Abestanis/BalloonLaserPointing/src/SerialConnection.cpp

#include "arduinoSystem.h"
#include "SerialConnection.h"


/** The first byte of a message header, used to detect the start of the header */
constexpr uint8_t SYNC_BYTE_1 = 0xAA;
/** The second byte of a message header, used to detect the start of the header */
constexpr uint8_t SYNC_BYTE_2 = 0x55;

/**
 * The structure of a GPS message.
 */
typedef struct [[gnu::packed]] {
    /** The latitude in degrees. */
    double latitude;
    /** The longitude in degrees. */
    double longitude;
    /** The height in meters. */
    double height;
} GpsMessage;

/**
 * The structure of a SetLocation message.
 */
typedef struct [[gnu::packed]] {
    /** The latitude in degrees. */
    double latitude;
    /** The longitude in degrees. */
    double longitude;
    /** The height in meters. */
    double height;
    /** The orientation in degrees from north. */
    double orientation;
} SetLocationMessage;

/**
 * The structure of a SetMotorPosition message.
 */
typedef struct [[gnu::packed]] {
    /** The motor that should be controlled. */
    SerialConnection::Motor motor;
    /** The target angle of the motor. */
    double angle;
} SetMotorPositionMessage;

/**
 * The structure of a SetCalibrationPoint message.
 */
typedef struct [[gnu::packed]] {
    /** The motor that should be calibrated. */
    SerialConnection::Motor motor;
} SetCalibrationPointMessage;

/** The start of every message. */
typedef struct [[gnu::packed]] {
    /** Synchronization bytes to allow to detect the start of a message. */
    uint8_t sync[2];
    /** The type of the message, that will be send directly after the header. */
    SerialConnection::MessageType type;
} MessageHeader;


SerialConnection::SerialConnection(CommandHandler& handler) : handler(handler) {
    Serial.begin(9600);
}

void SerialConnection::fetchMessages() {
    size_t expectedSize = 0;
    switch (nextMessageType) {
    case PING:
    case CALIBRATE_MOTORS:
        break;
    case GPS:
        expectedSize = sizeof(GpsMessage);
        break;
    case SET_LOCATION:
        expectedSize = sizeof(SetLocationMessage);
        break;
    case SET_MOTOR_POSITION:
        expectedSize = sizeof(SetMotorPositionMessage);
        break;
    case SET_CALIBRATION_POINT:
        expectedSize = sizeof(SetCalibrationPointMessage);
        break;
    case HEADER:
        expectedSize = sizeof(MessageHeader);
        break;
    }
    if ((size_t) Serial.available() < expectedSize) {
        return;
    }
    switch (nextMessageType) {
    case PING:
        handler.handlePing();
        break;
    case GPS:
        GpsMessage gpsData;
        Serial.readBytes(reinterpret_cast<uint8_t*>(&gpsData), sizeof(gpsData));
        handler.handleGps(deg_t(gpsData.latitude), deg_t(gpsData.longitude),
                meter_t(gpsData.height));
        break;
    case CALIBRATE_MOTORS:
        handler.handleMotorsCalibration();
        break;
    case SET_LOCATION:
        SetLocationMessage setLocationData;
        Serial.readBytes(reinterpret_cast<uint8_t*>(&setLocationData), sizeof(setLocationData));
        handler.handleSetLocation(deg_t(setLocationData.latitude), deg_t(setLocationData.longitude),
                meter_t(setLocationData.height), deg_t(setLocationData.orientation));
        break;
    case SET_MOTOR_POSITION:
        SetMotorPositionMessage setMotorPositionData;
        Serial.readBytes(reinterpret_cast<uint8_t*>(&setMotorPositionData),
                sizeof(setMotorPositionData));
        handler.handleSetMotorPosition(setMotorPositionData.motor,
                deg_t(setMotorPositionData.angle));
        break;
    case SET_CALIBRATION_POINT:
        SetCalibrationPointMessage setCalibrationPointData;
        Serial.readBytes(reinterpret_cast<uint8_t*>(&setCalibrationPointData),
                sizeof(setCalibrationPointData));
        handler.handleSetCalibrationPoint(setCalibrationPointData.motor);
        break;
    case HEADER:
        if (Serial.read() != SYNC_BYTE_1 || Serial.read() != SYNC_BYTE_2) {
            // Short circuit return to avoid consuming
            // a potential valid sync sequence after an invalid one.
            return;
        }
        MessageHeader header;
        Serial.readBytes(reinterpret_cast<uint8_t*>(&header) + sizeof(header.sync),
                expectedSize - sizeof(header.sync));
        nextMessageType = header.type;
        return; // Don't set the type back to HEADER, return early.
    }
    nextMessageType = HEADER;
}
