Abestanis/BalloonLaserPointing/include/types.h

/**
 * Shared types
 */

#pragma once

#include "Vec3.h"
#include "units.h"

/**
 * A position in a 3 dimensional space.
 */
typedef Vec3<meter_t> Position;

/**
 * A 3 dimensional double vector.
 */
typedef Vec3<double> Vec3D;
