Abestanis/BalloonLaserPointing/src/Pins.cpp

#include "Pins.h"

constexpr Pin Pins::baseMotor1;
constexpr Pin Pins::baseMotor2;
constexpr Pin Pins::baseMotor3;
constexpr Pin Pins::baseMotor4;
constexpr Pin Pins::baseMotorCalibration;
constexpr Pin Pins::elevationMotor1;
constexpr Pin Pins::elevationMotor2;
constexpr Pin Pins::elevationMotor3;
constexpr Pin Pins::elevationMotor4;
constexpr Pin Pins::elevationMotorCalibration;
